ImpulseRC/OSD/images/Apex_OSD/Apex_OSD.jpg

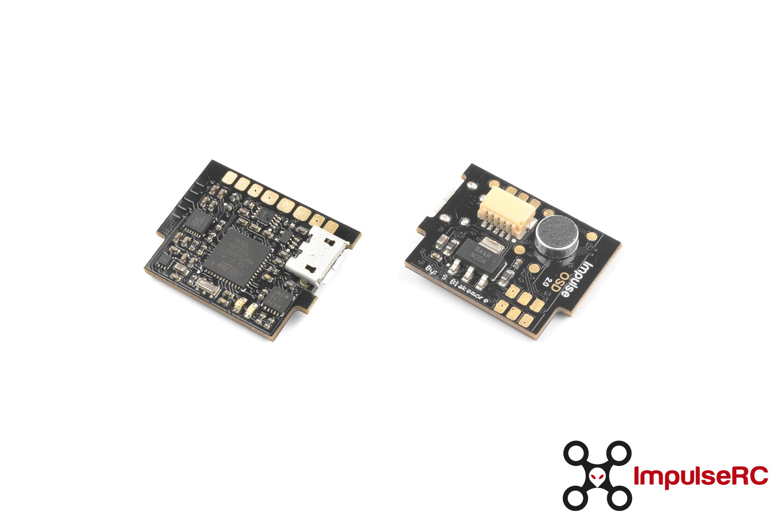
images/Apex_OSD/Apex_OSD.jpg
