ImpulseRC/OSD/images/ConfigTool/Activation.jpg

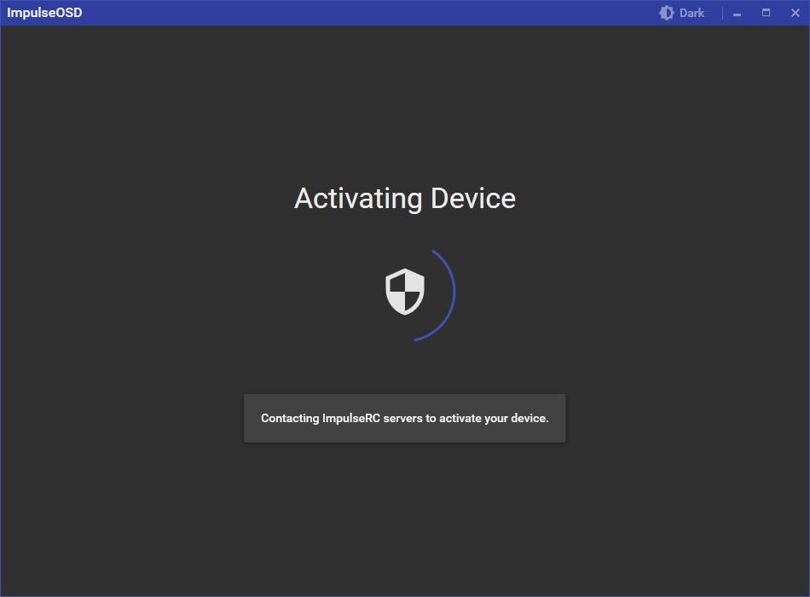
images/ConfigTool/Activation.jpg
