ImpulseRC/OSD/images/ConfigTool/Bootloader.jpg

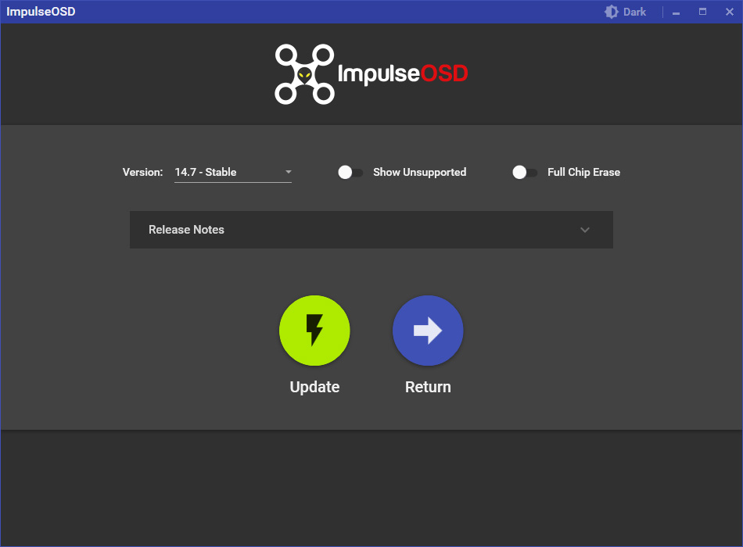
images/ConfigTool/Bootloader.jpg
