ImpulseRC/OSD/images/ConfigTool/DarkTheme.jpg

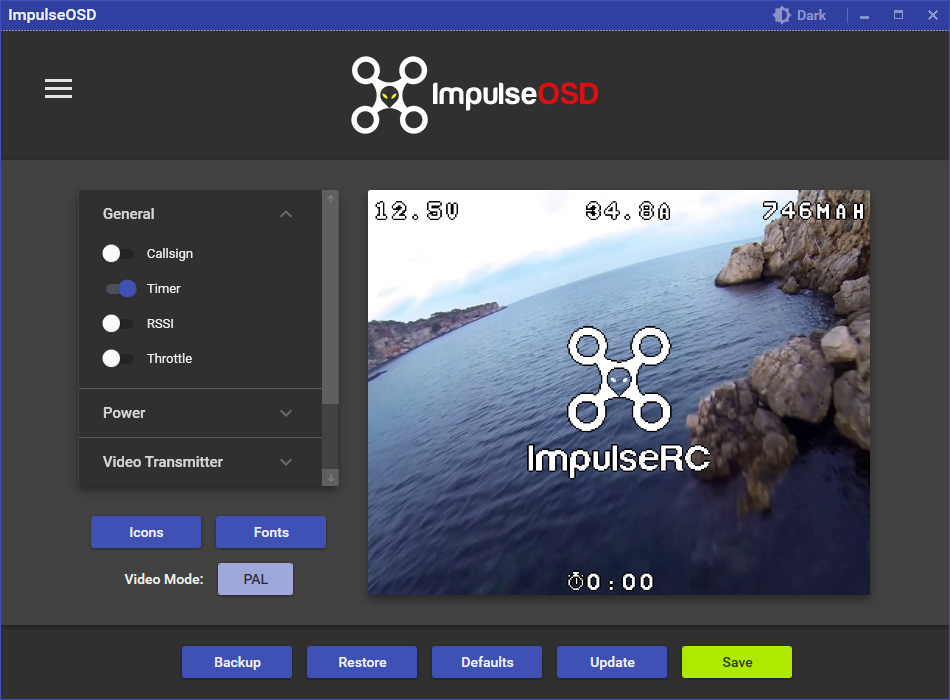
images/ConfigTool/DarkTheme.jpg
