ImpulseRC/OSD/images/ConfigTool/DragDrop.jpg

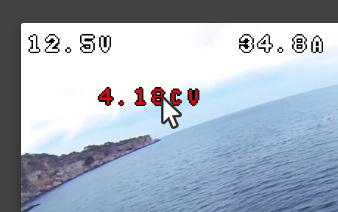
images/ConfigTool/DragDrop.jpg
