ImpulseRC/OSD/images/ConfigTool/Flashing.jpg

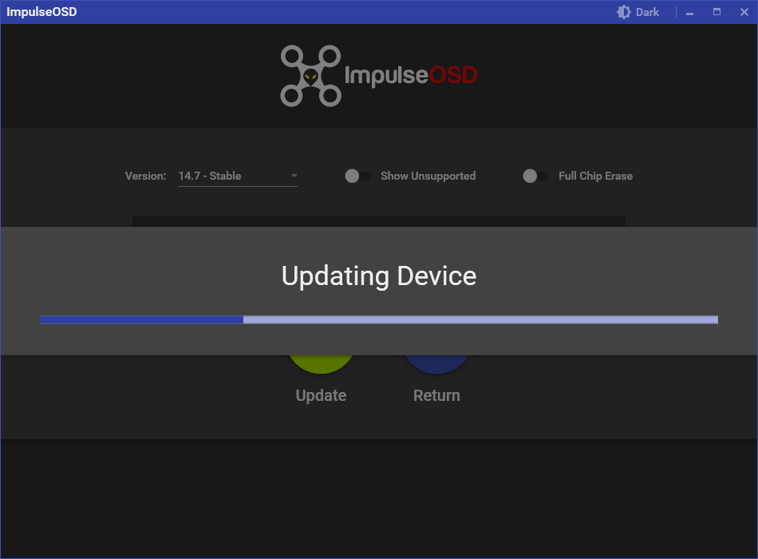
images/ConfigTool/Flashing.jpg
