ImpulseRC/OSD/images/ConfigTool/Fonts.jpg

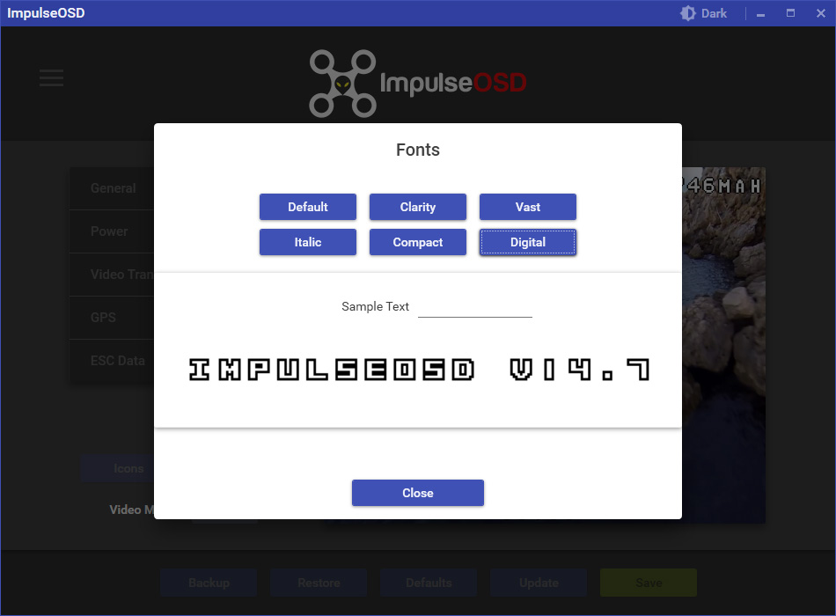
images/ConfigTool/Fonts.jpg
