ImpulseRC/OSD/images/ConfigTool/GeneralSettings.jpg

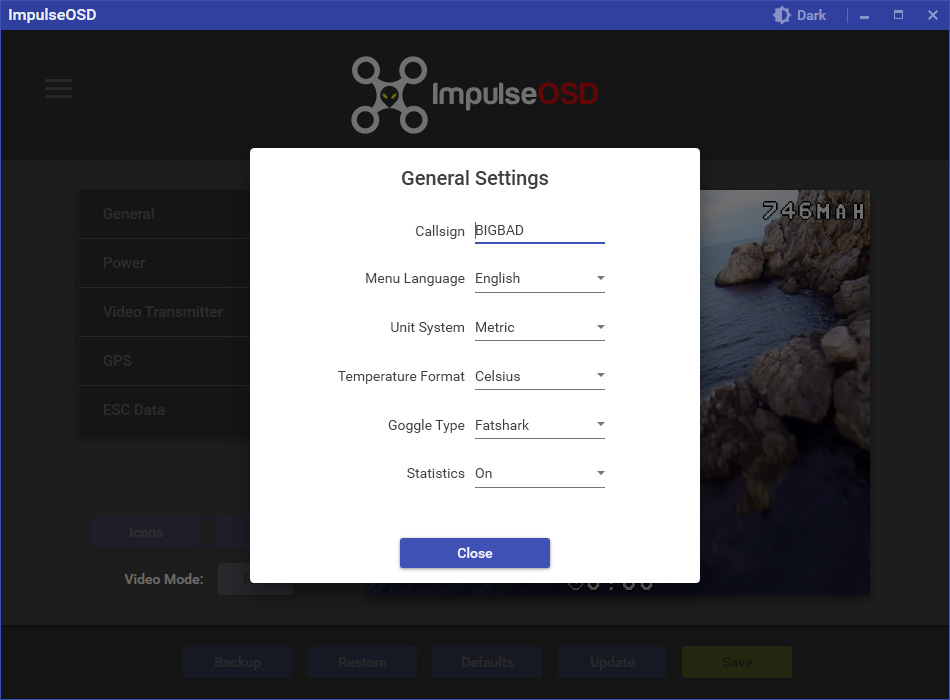
images/ConfigTool/GeneralSettings.jpg
