ImpulseRC/OSD/images/ConfigTool/LightTheme.jpg

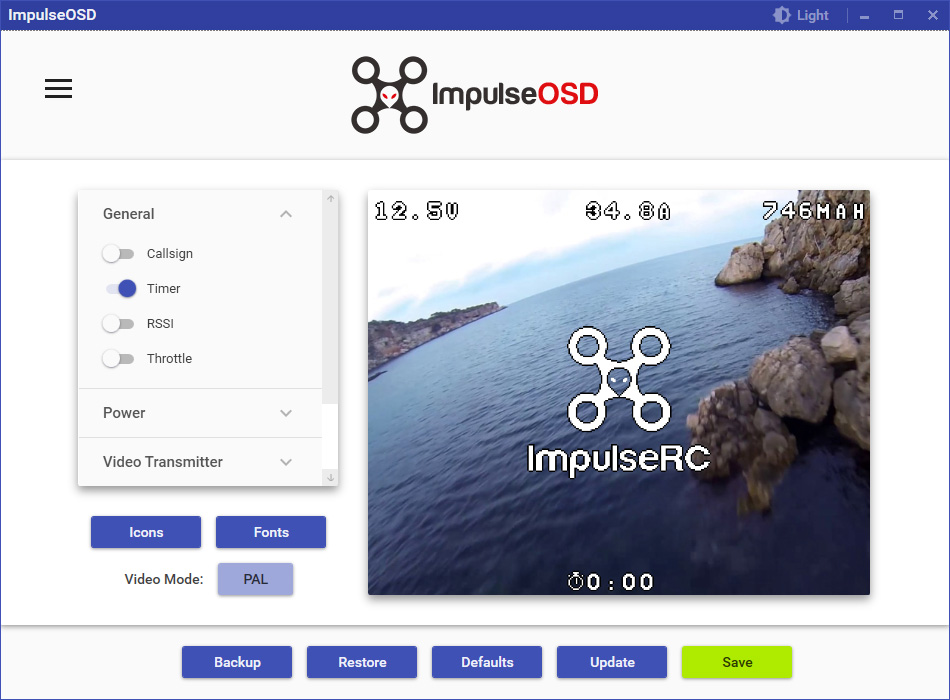
images/ConfigTool/LightTheme.jpg
