ImpulseRC/OSD/images/ConfigTool/Mac.jpg

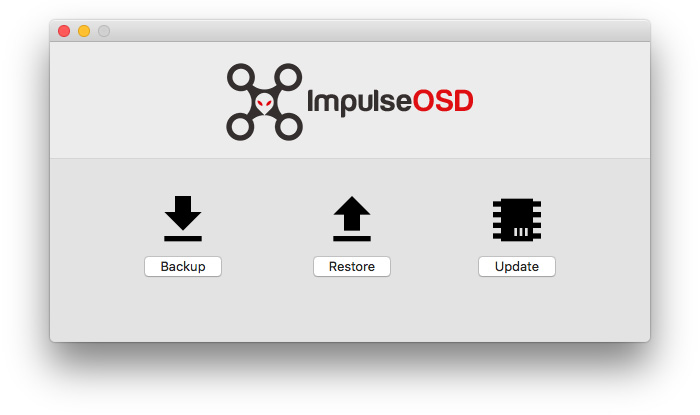
images/ConfigTool/Mac.jpg
