ImpulseRC/OSD/images/ConfigTool/MacConnection.jpg

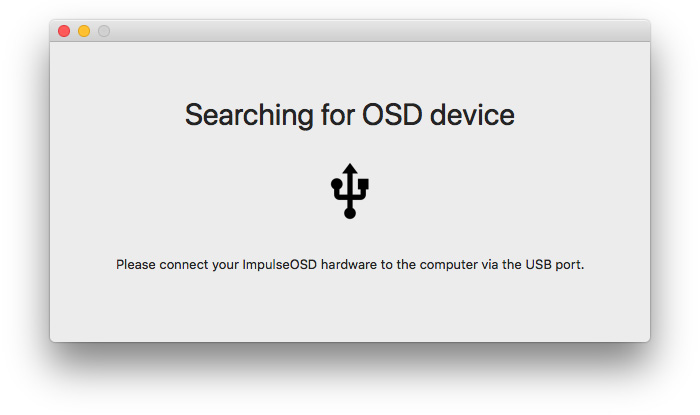
images/ConfigTool/MacConnection.jpg
