ImpulseRC/OSD/images/ConfigTool/MacStartup.jpg

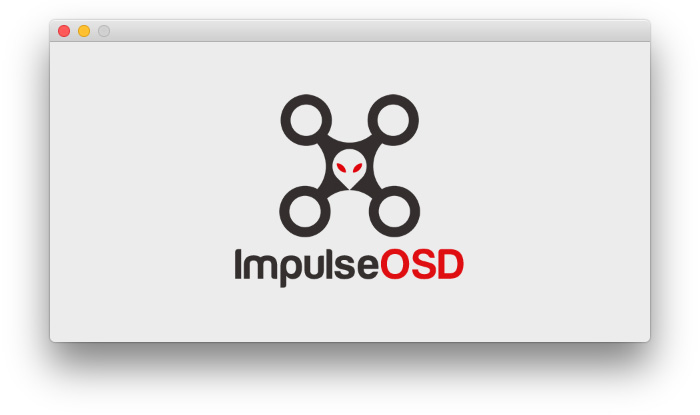
images/ConfigTool/MacStartup.jpg
