ImpulseRC/OSD/images/ConfigTool/OsdLabels.jpg

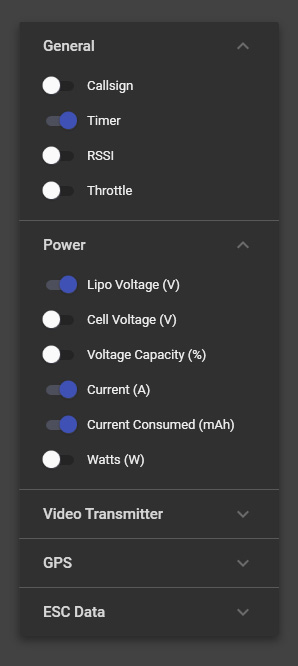
images/ConfigTool/OsdLabels.jpg
