ImpulseRC/OSD/images/ConfigTool/ReducedFunctionality.jpg

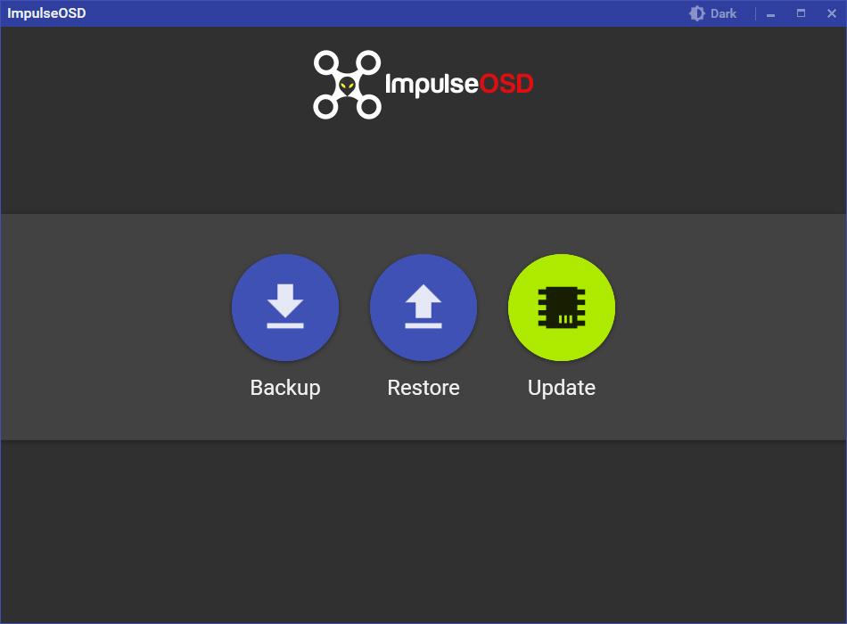
images/ConfigTool/ReducedFunctionality.jpg
