ImpulseRC/OSD/images/ConfigTool/SettingsPanel.jpg

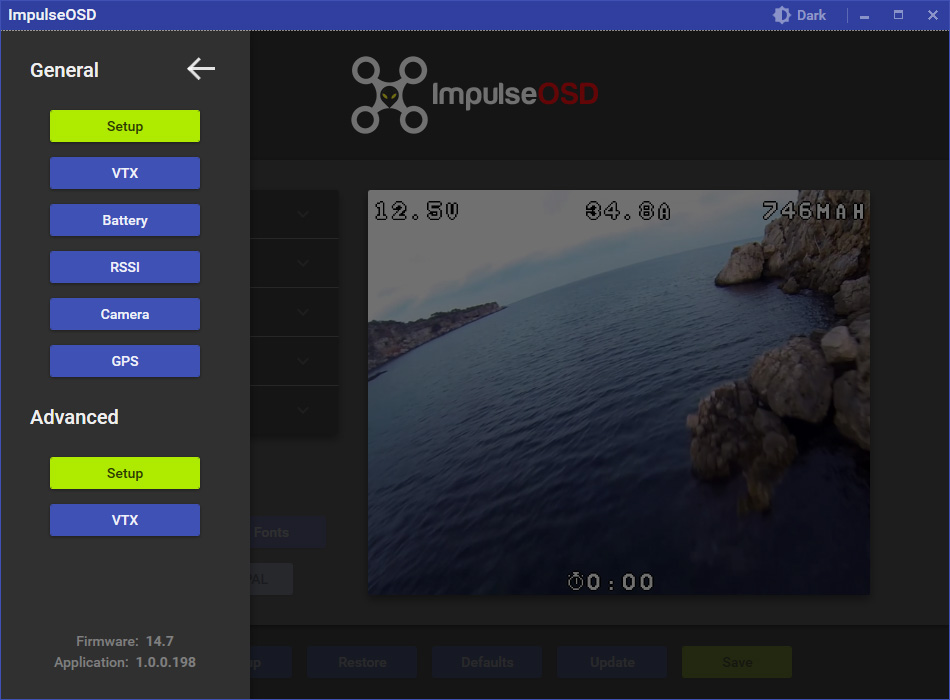
images/ConfigTool/SettingsPanel.jpg
