ImpulseRC/OSD/images/ConfigTool/SettingsPanelButton.jpg

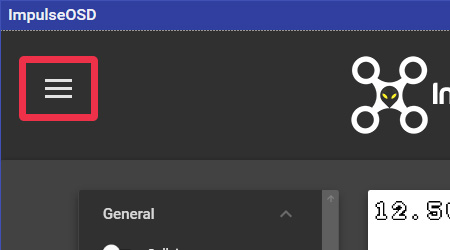
images/ConfigTool/SettingsPanelButton.jpg
