ImpulseRC/OSD/images/ConfigTool/Updating.jpg

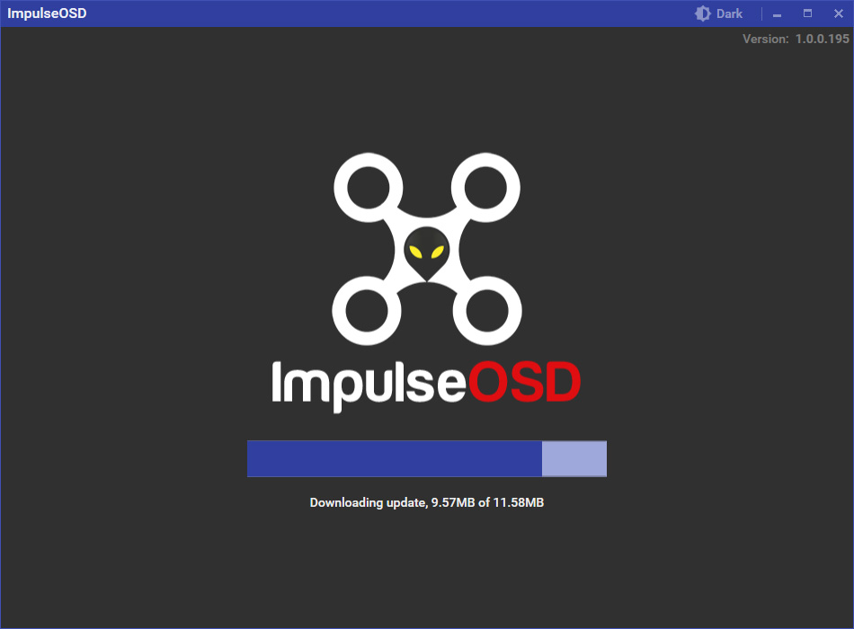
images/ConfigTool/Updating.jpg
