ImpulseRC/OSD/images/ConfigTool/Version.jpg

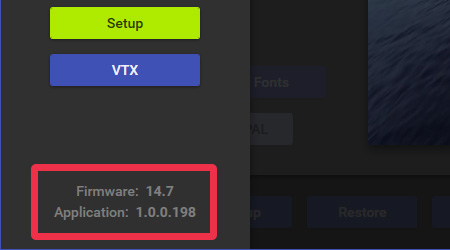
images/ConfigTool/Version.jpg
