ImpulseRC/OSD/images/Wolf/Wolf_PDB.jpg

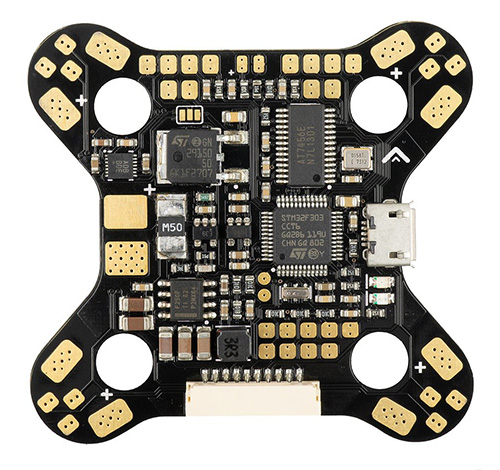
images/Wolf/Wolf_PDB.jpg
