ImpulseRC/OSD/images/Wolf/Wolf_Rev2.png

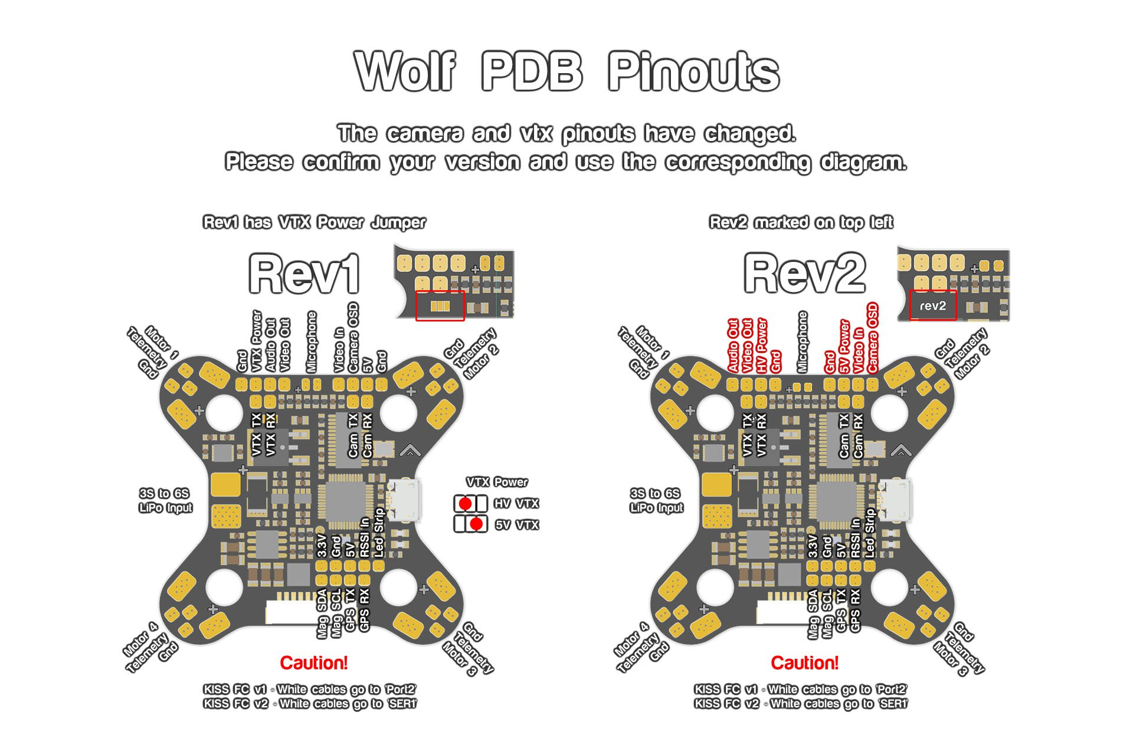
images/Wolf/Wolf_Rev2.png
