ImpulseRC/OSD/images/Wolf/Wolf_Rev3.png

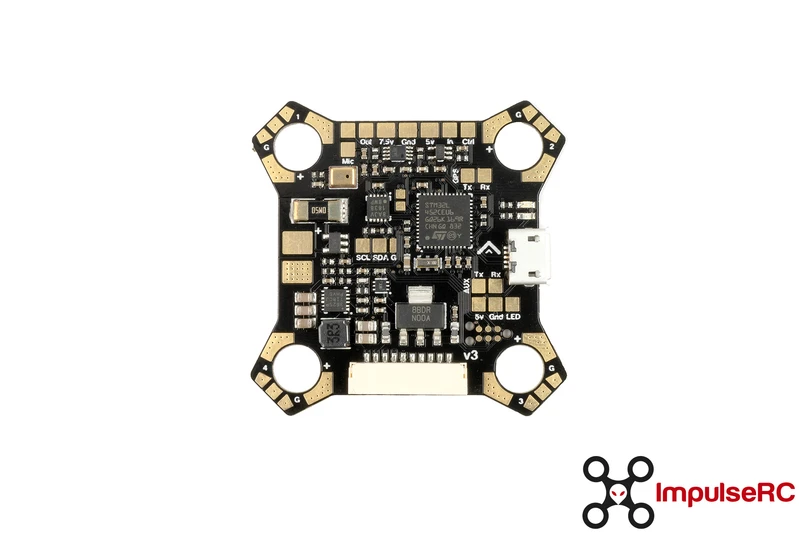
images/Wolf/Wolf_Rev3.png
