ImpulseRC/OSD/images/Wolf/WolfV3_BF_Pinout.jpg

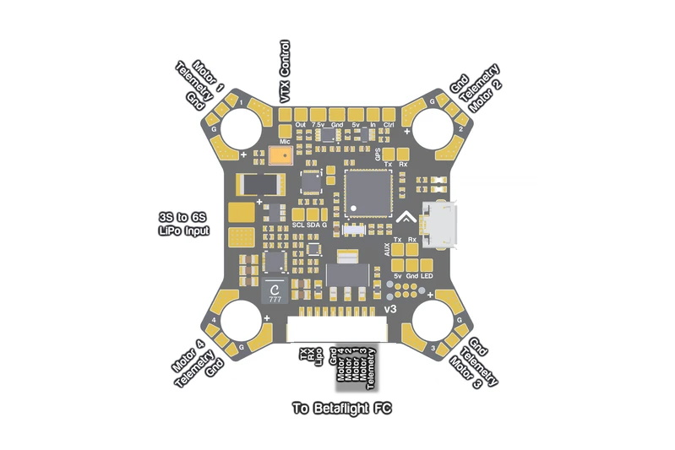
images/Wolf/WolfV3_BF_Pinout.jpg
